Chrismettal/MiniMarquee/3D/PCB/v0.1/v0.1RenderBack.png

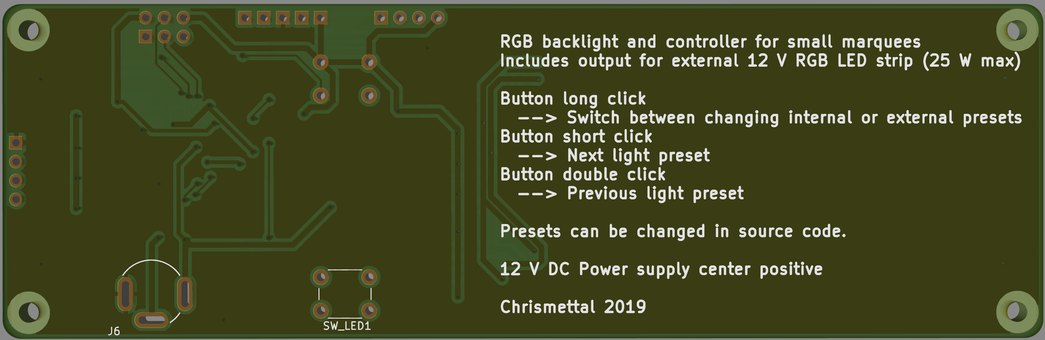
3D/PCB/v0.1/v0.1RenderBack.png
