Chrismettal/MiniMarquee/images/DC_Jack.jpg

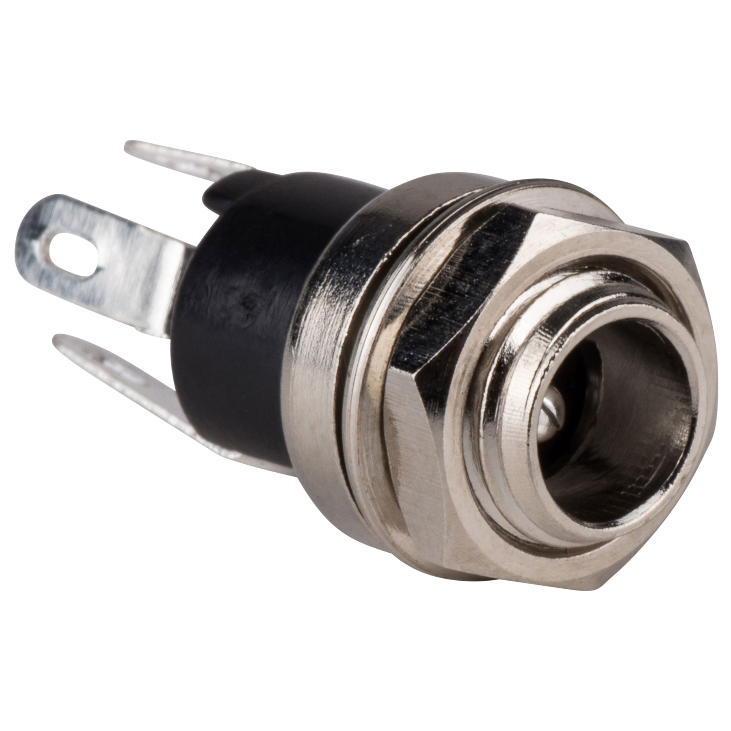
images/DC_Jack.jpg
