Chrismettal/MiniMarquee/images/PCB_placemap.png

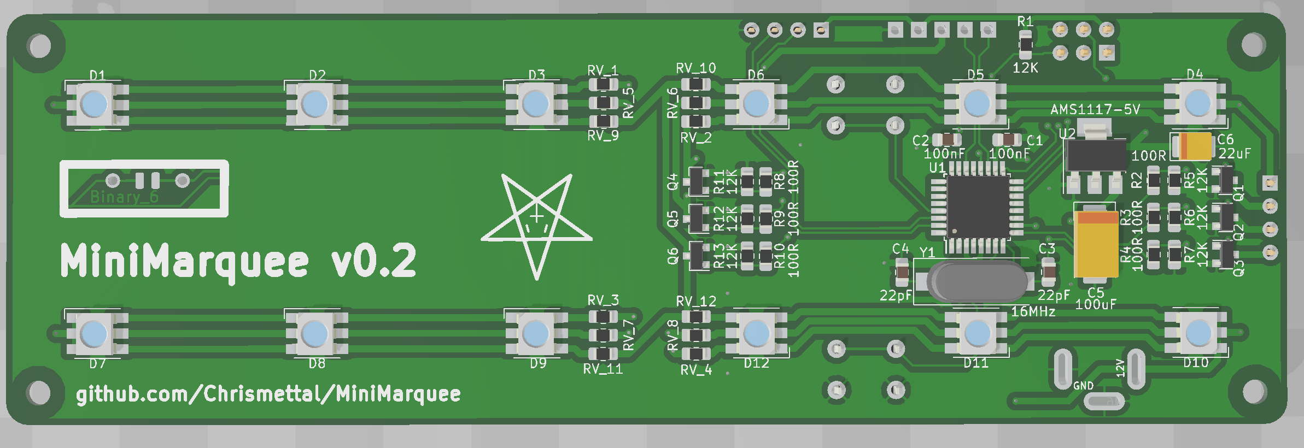
images/PCB_placemap.png
