Chrismettal/MiniMarquee/images/PCB_render1.png

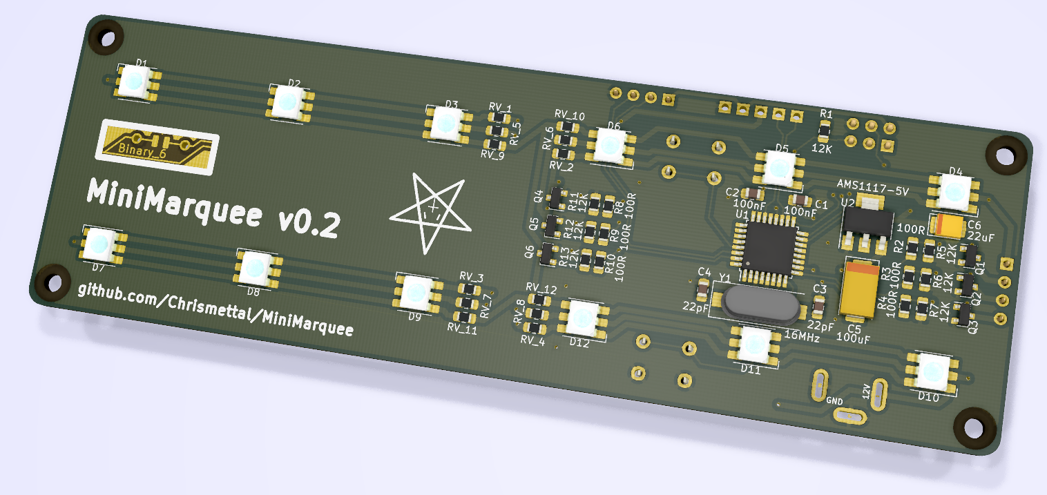
images/PCB_render1.png
