Chrismettal/MiniMarquee/images/PCB_render2.png

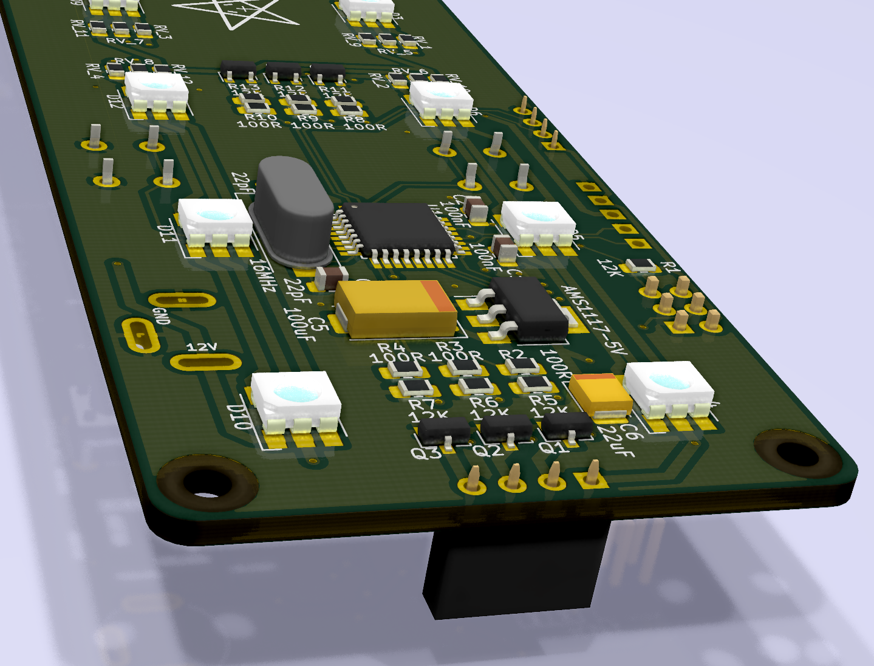
images/PCB_render2.png
