Chrismettal/MiniMarquee/3D/Printable_v0.2/Sony/PS2/PS2_clr.stl

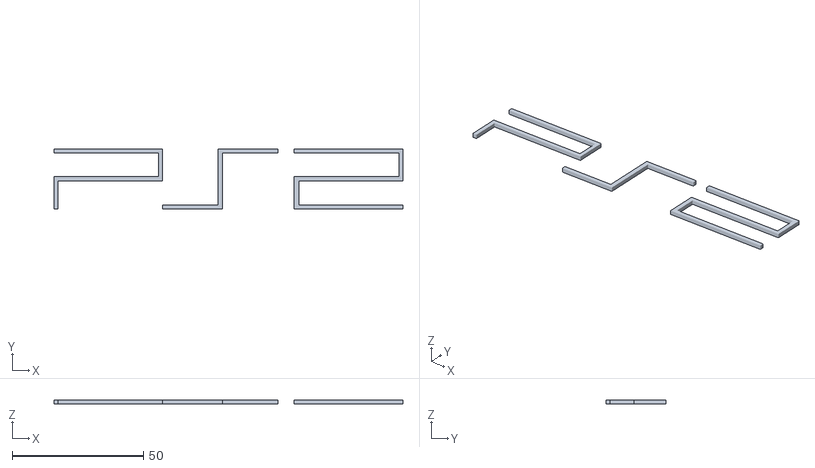
[picture p48: CAD file, 2019-06-09]
3D/Printable_v0.2/Sony/PS2/PS2_clr.stl
133.1 x 23.0 x 1.60
