Chrismettal/MiniMarquee/3D/Printable_v0.2/Sony/PS4/PS4_blu.stl

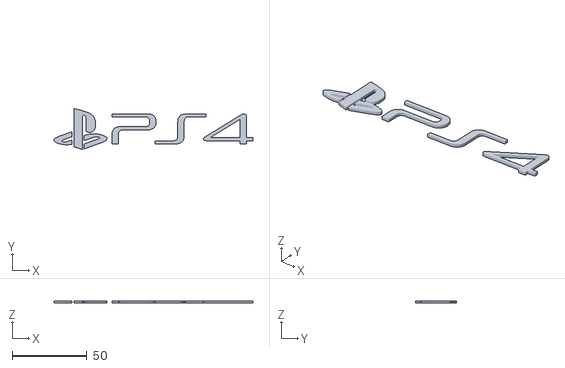
[picture p50: CAD file, 2019-06-01]
3D/Printable_v0.2/Sony/PS4/PS4_blu.stl
133.6 x 27.5 x 1.60
