Chrismettal/MiniMarquee/3D/Printable_v0.2/Atari/2600/2600_clr.stl

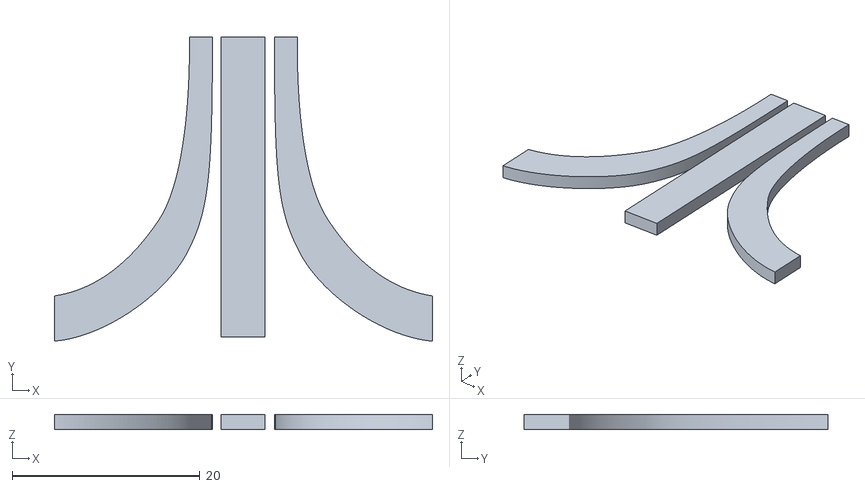
[picture p51: CAD file, 2019-06-20]
3D/Printable_v0.2/Atari/2600/2600_clr.stl
40.3 x 32.4 x 1.60
