Chrismettal/MiniMarquee/3D/Printable_v0.2/Diffusor_wh.stl

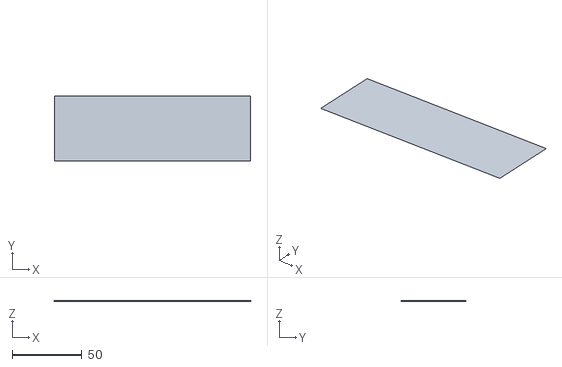
[picture p52: CAD file, 2019-06-21]
3D/Printable_v0.2/Diffusor_wh.stl
140.4 x 46.4 x 0.2
