Chrismettal/MiniMarquee/3D/Printable_v0.2/Microsoft/Xbox/Xbox_grn.stl

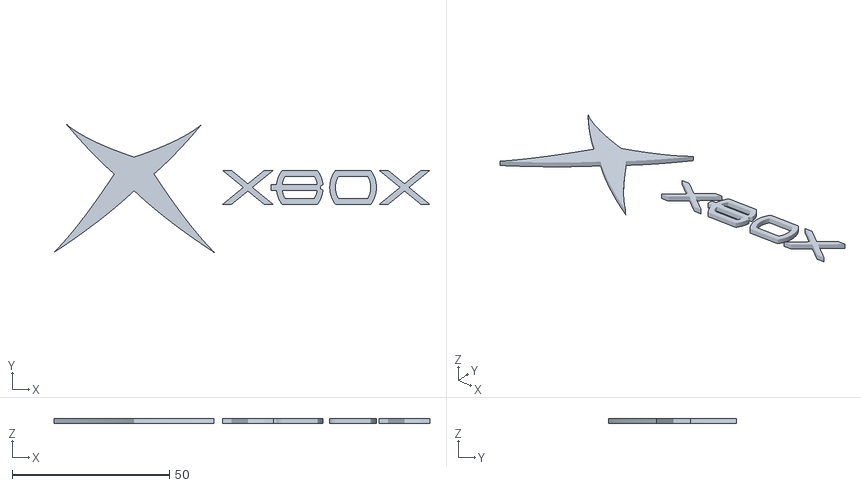
[picture p53: CAD file, 2019-06-10]
3D/Printable_v0.2/Microsoft/Xbox/Xbox_grn.stl
119.7 x 40.6 x 1.60
