Chrismettal/MiniMarquee/3D/Printable_v0.2/Microsoft/Xbox360/Xbox360_grn.stl

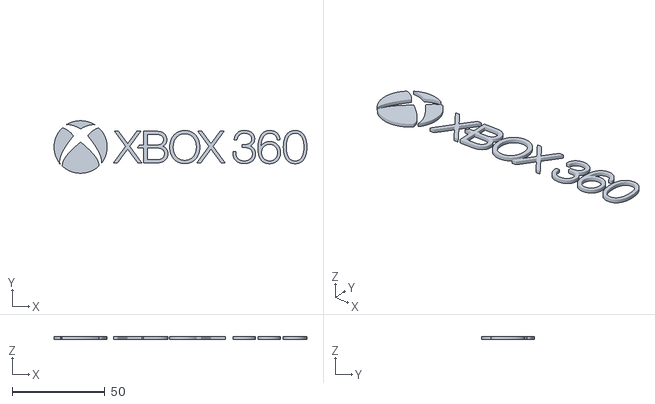
[picture p54: CAD file, 2019-06-10]
3D/Printable_v0.2/Microsoft/Xbox360/Xbox360_grn.stl
136.6 x 28.4 x 1.60
