Chrismettal/MiniMarquee/3D/Printable_v0.2/Nintendo/N64/N64_grn.stl

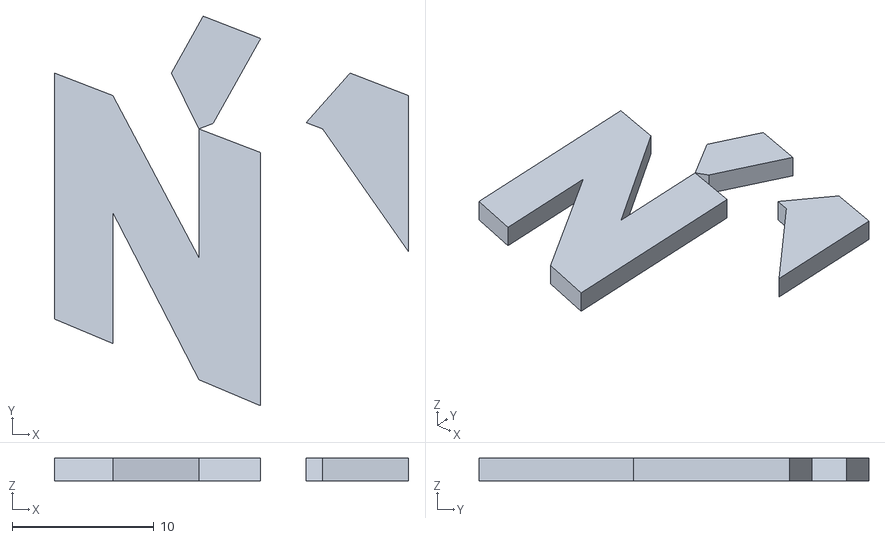
[picture p55: CAD file, 2019-06-09]
3D/Printable_v0.2/Nintendo/N64/N64_grn.stl
24.9 x 27.5 x 1.60
