Chrismettal/MiniMarquee/3D/Printable_v0.2/Nintendo/NES/NES_red.stl

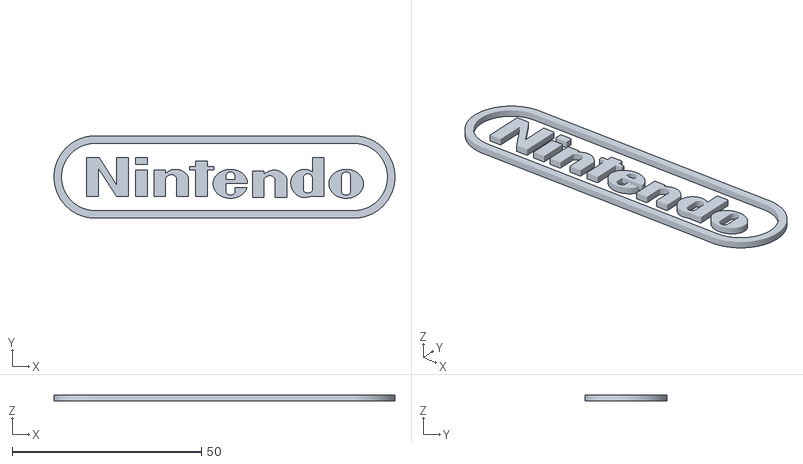
[picture p56: CAD file, 2019-06-09]
3D/Printable_v0.2/Nintendo/NES/NES_red.stl
90.0 x 21.7 x 1.60
