Chrismettal/MiniMarquee/3D/Printable_v0.2/Nintendo/SNES/SNES_wh.stl

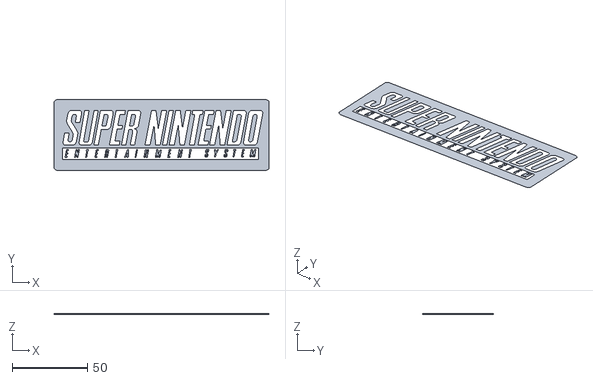
[picture p57: CAD file, 2019-06-09]
3D/Printable_v0.2/Nintendo/SNES/SNES_wh.stl
143.0 x 47.2 x 0.2
