Chrismettal/MiniMarquee/3D/Printable_v0.2/Nintendo/Wii/Wii_blk.stl

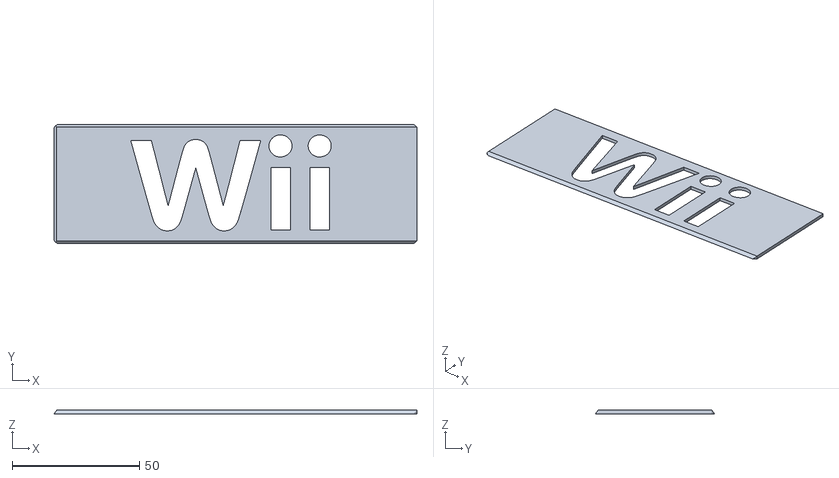
[picture p58: CAD file, 2019-06-09]
3D/Printable_v0.2/Nintendo/Wii/Wii_blk.stl
142.9 x 46.9 x 1.40
