Chrismettal/MiniMarquee/3D/Printable_v0.2/Nintendo/WiiU/WiiU_clr.stl

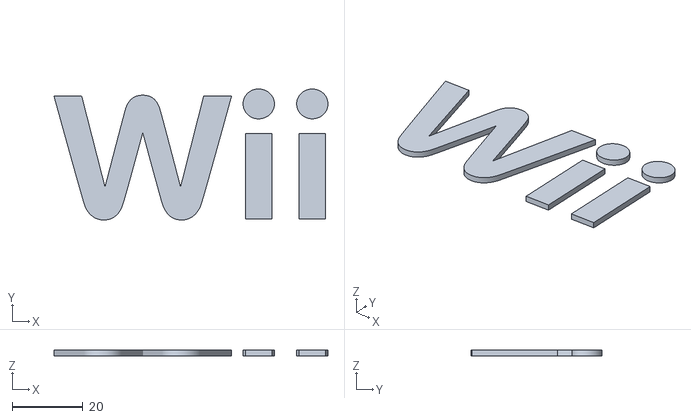
[picture p59: CAD file, 2019-06-09]
3D/Printable_v0.2/Nintendo/WiiU/WiiU_clr.stl
77.6 x 37.1 x 1.60
