Chrismettal/MiniMarquee/3D/Printable_v0.2/Sega/MasterSystem/Sega_MS_red.stl

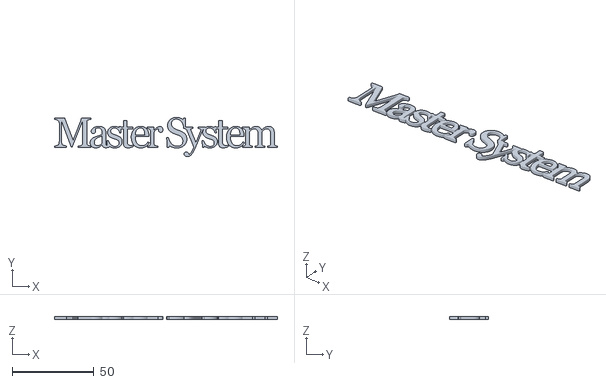
[picture p60: CAD file, 2019-06-20]
3D/Printable_v0.2/Sega/MasterSystem/Sega_MS_red.stl
136.0 x 24.0 x 1.60
