Chrismettal/MiniMarquee/3D/Printable_v0.2/Sony/PS2/PS2_wh.stl

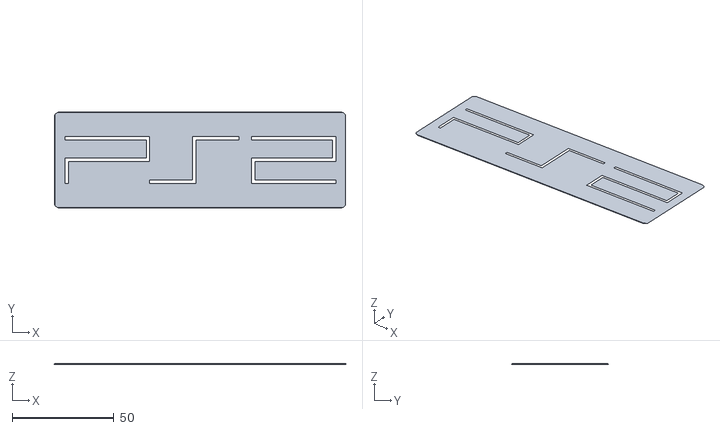
[picture p61: CAD file, 2019-06-09]
3D/Printable_v0.2/Sony/PS2/PS2_wh.stl
143.0 x 47.2 x 0.2
