Chrismettal/MiniMarquee/3D/Printable_v0.2/Microsoft/XboxOne/XboxOne_grn.stl

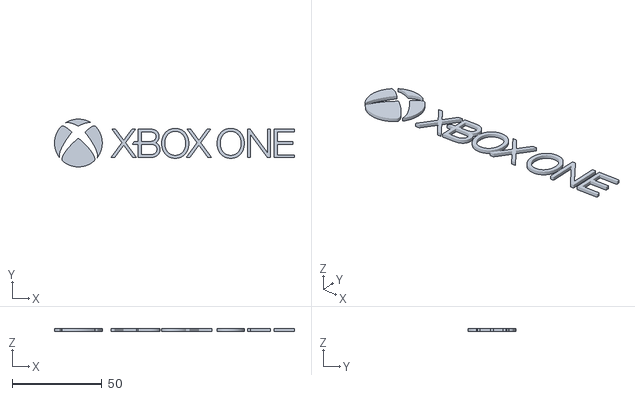
[picture p62: CAD file, 2019-06-10]
3D/Printable_v0.2/Microsoft/XboxOne/XboxOne_grn.stl
133.5 x 26.6 x 1.60
