Chrismettal/MiniMarquee/3D/Printable_v0.2/NeoGeo/NeoGeo_red.stl

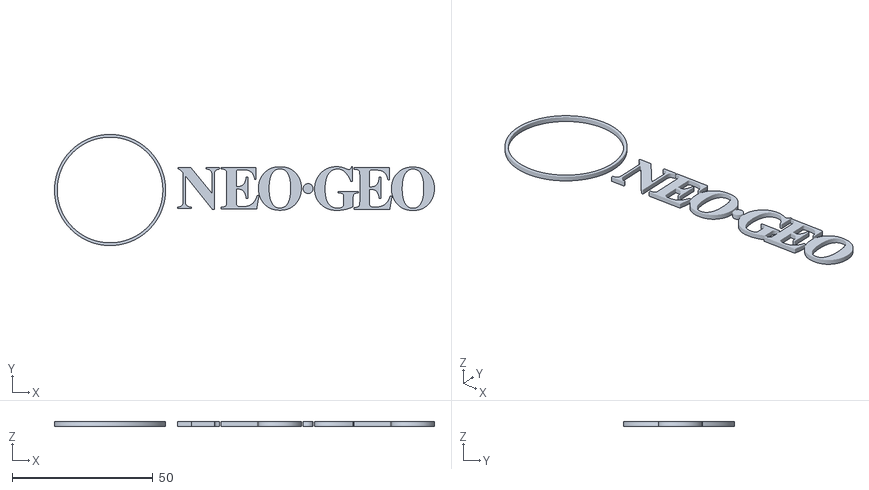
[picture p63: CAD file, 2019-06-20]
3D/Printable_v0.2/NeoGeo/NeoGeo_red.stl
134.9 x 39.4 x 1.60
