Chrismettal/MiniMarquee/3D/Printable_v0.2/Nintendo/GC/GC_blu.stl

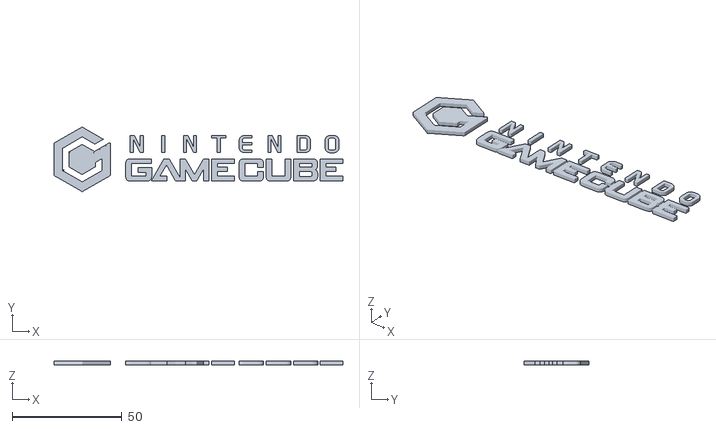
[picture p64: CAD file, 2019-06-09]
3D/Printable_v0.2/Nintendo/GC/GC_blu.stl
131.4 x 29.5 x 1.60
