Chrismettal/MiniMarquee/3D/Printable_v0.2/Nintendo/N64/N64_blk.stl

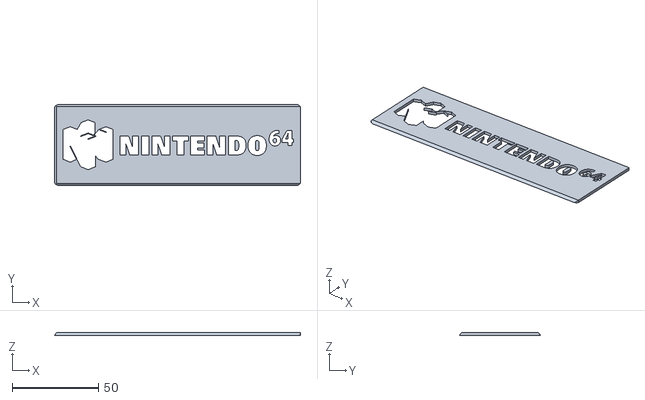
[picture p65: CAD file, 2019-06-09]
3D/Printable_v0.2/Nintendo/N64/N64_blk.stl
143.0 x 47.2 x 1.60
