Chrismettal/MiniMarquee/3D/Printable_v0.2/Nintendo/WiiU/WiiU_blk.stl

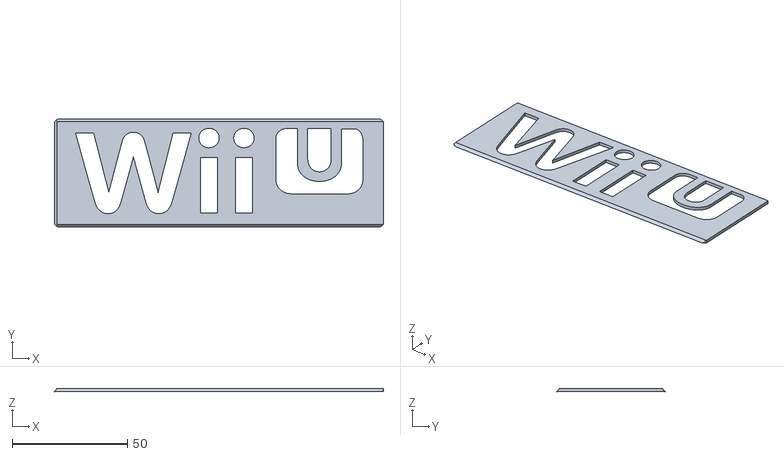
[picture p66: CAD file, 2019-06-09]
3D/Printable_v0.2/Nintendo/WiiU/WiiU_blk.stl
142.9 x 46.9 x 1.40
