Chrismettal/MiniMarquee/3D/Printable_v0.2/RawSign_blk.stl

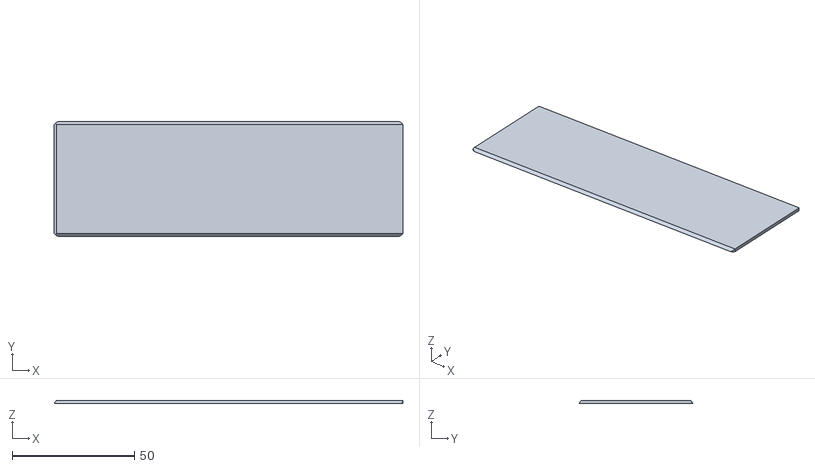
[picture p67: CAD file, 2019-06-10]
3D/Printable_v0.2/RawSign_blk.stl
142.9 x 46.9 x 1.40
