Chrismettal/MiniMarquee/3D/Printable_v0.2/Sony/PS1/PS1_blu.stl

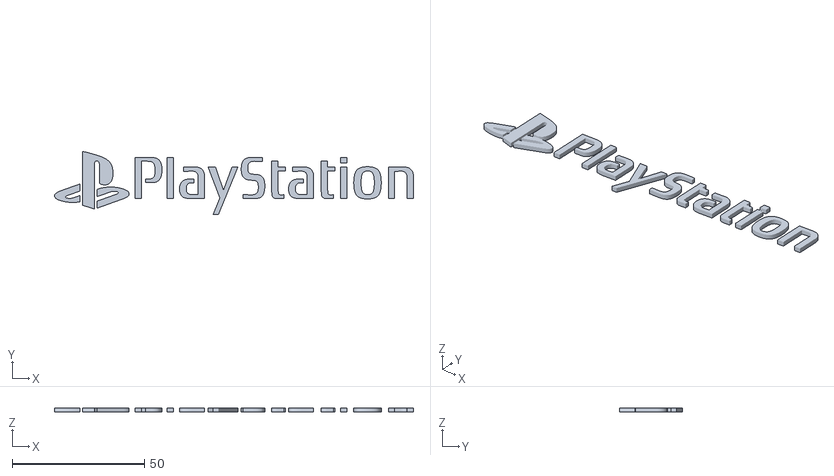
[picture p68: CAD file, 2019-06-09]
3D/Printable_v0.2/Sony/PS1/PS1_blu.stl
135.5 x 23.9 x 1.60
