Chrismettal/MiniMarquee/3D/Printable_v0.2/Sony/PS3/PS3_clr.stl

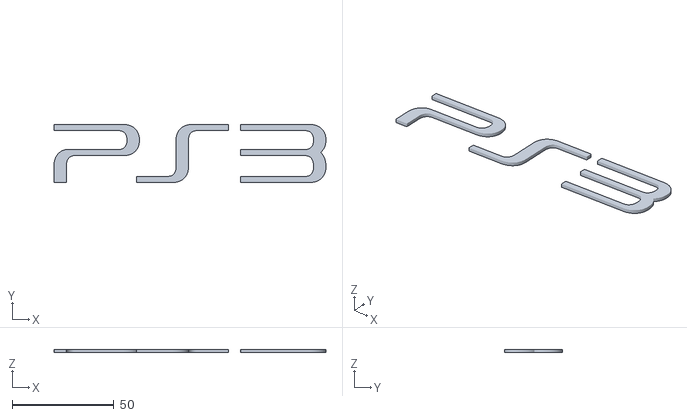
[picture p69: CAD file, 2019-06-09]
3D/Printable_v0.2/Sony/PS3/PS3_clr.stl
133.6 x 28.5 x 1.60
