Chrismettal/MiniMarquee/3D/Printable_v0.2/Commodore/Com_blu.stl

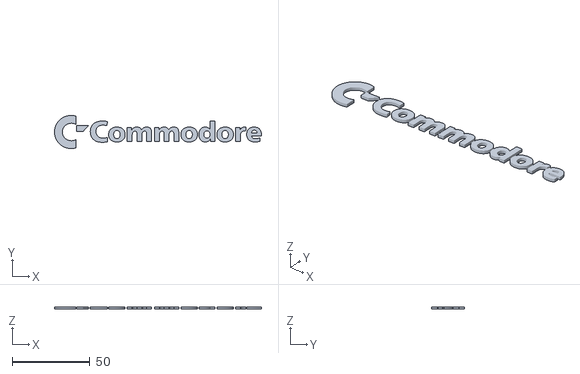
[picture p70: CAD file, 2019-06-20]
3D/Printable_v0.2/Commodore/Com_blu.stl
133.1 x 21.3 x 1.60
