Chrismettal/MiniMarquee/3D/Printable_v0.2/Nintendo/N64/N64_blu.stl

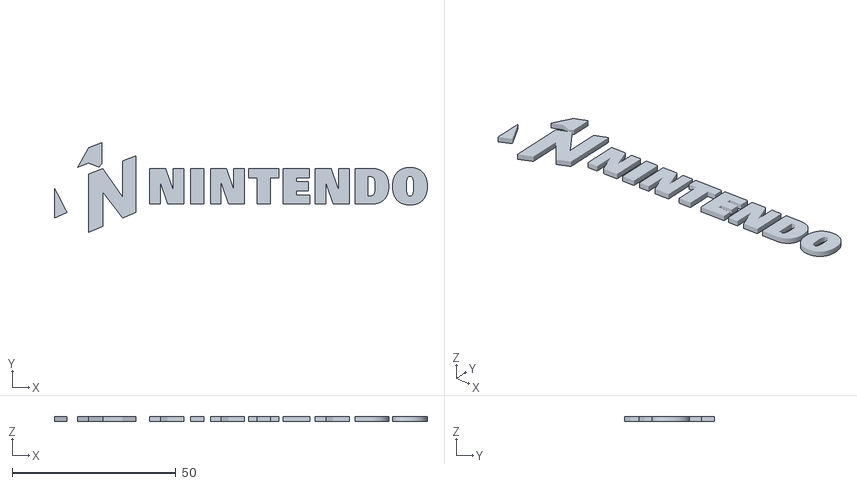
[picture p71: CAD file, 2019-06-09]
3D/Printable_v0.2/Nintendo/N64/N64_blu.stl
114.0 x 27.4 x 1.60
