Chrismettal/MiniMarquee/3D/Printable_v0.2/Nintendo/NES/NES_clr.stl

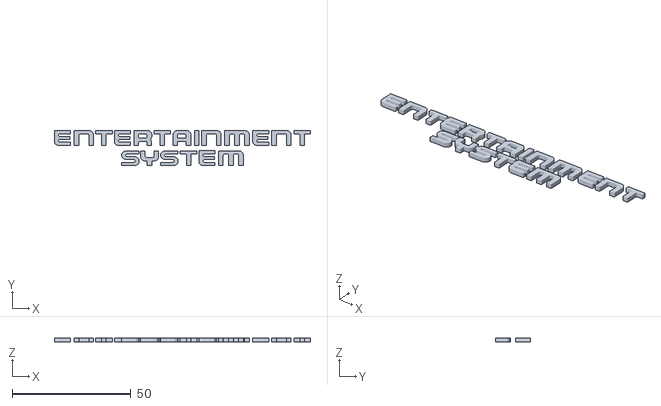
[picture p72: CAD file, 2019-06-09]
3D/Printable_v0.2/Nintendo/NES/NES_clr.stl
108.0 x 14.8 x 1.60
