Chrismettal/MiniMarquee/3D/Printable_v0.2/Nintendo/WiiU/WiiU_blu.stl

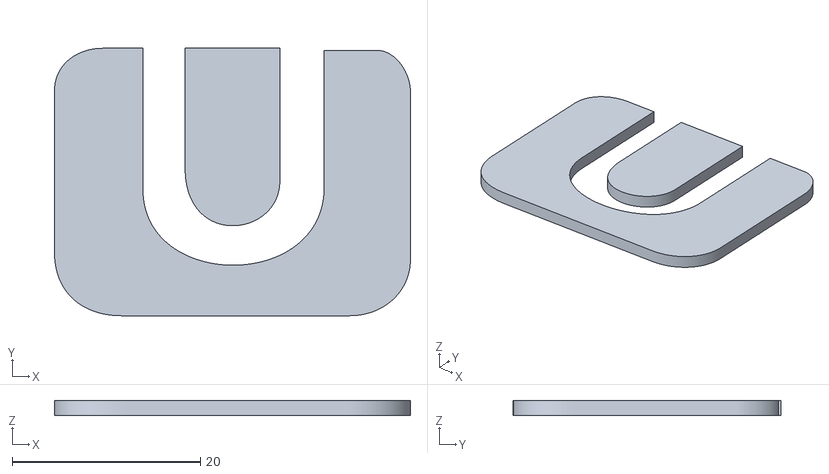
[picture p73: CAD file, 2019-06-09]
3D/Printable_v0.2/Nintendo/WiiU/WiiU_blu.stl
37.8 x 28.4 x 1.60
