Chrismettal/MiniMarquee/3D/Printable_v0.2/RawSign_wh.stl

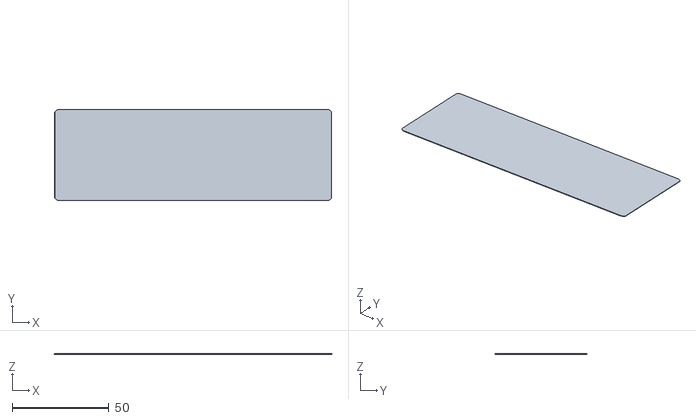
[picture p74: CAD file, 2019-06-10]
3D/Printable_v0.2/RawSign_wh.stl
143.0 x 47.2 x 0.2
