Chrismettal/MiniMarquee/3D/Printable_v0.2/Sega/MasterSystem/Sega_MS_blu.stl

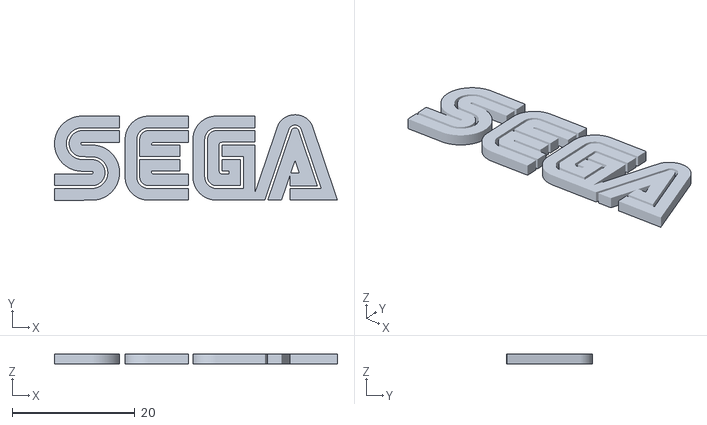
[picture p75: CAD file, 2019-06-20]
3D/Printable_v0.2/Sega/MasterSystem/Sega_MS_blu.stl
46.1 x 13.9 x 1.60
