Chrismettal/MiniMarquee/3D/Printable_v0.2/NeoGeo/NeoGeo_yel.stl

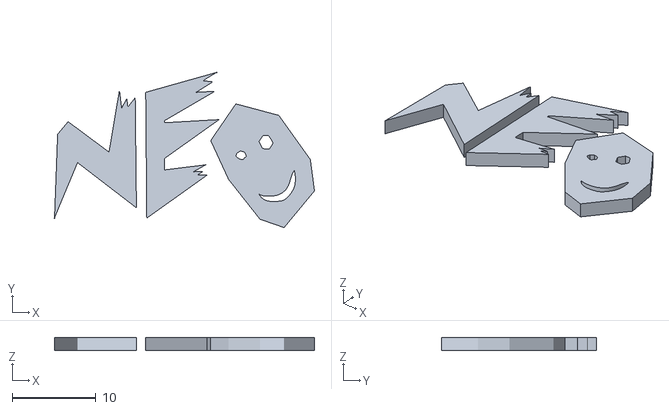
[picture p76: CAD file, 2019-06-20]
3D/Printable_v0.2/NeoGeo/NeoGeo_yel.stl
31.0 x 18.5 x 1.60
