Chrismettal/MiniMarquee/3D/Printable_v0.2/Nintendo/N64/N64_red.stl

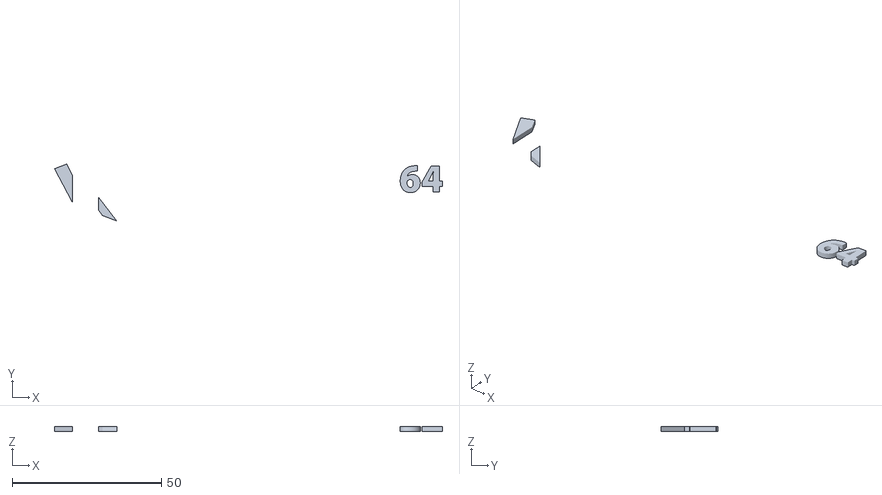
[picture p77: CAD file, 2019-06-09]
3D/Printable_v0.2/Nintendo/N64/N64_red.stl
129.8 x 19.1 x 1.60
