Chrismettal/MiniMarquee/images/Manual1.jpg

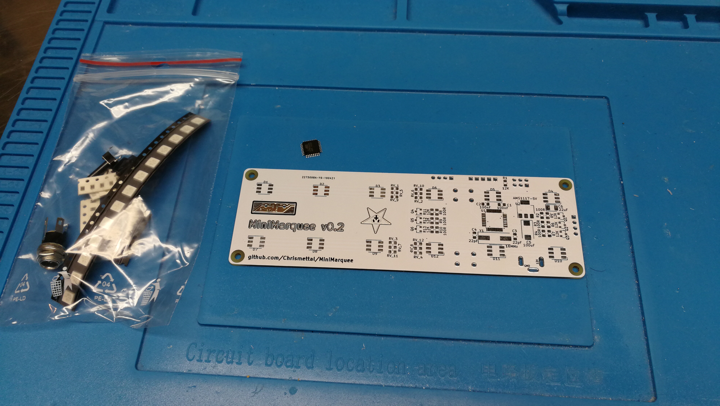
images/Manual1.jpg
