Chrismettal/MiniMarquee/images/Manual3.jpg

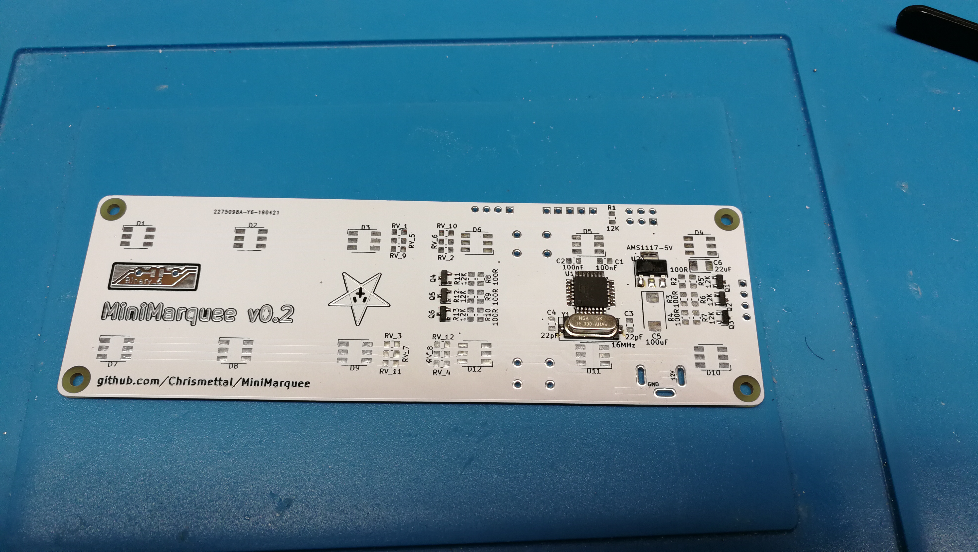
images/Manual3.jpg
