Chrismettal/MiniMarquee/images/Manual5.jpg

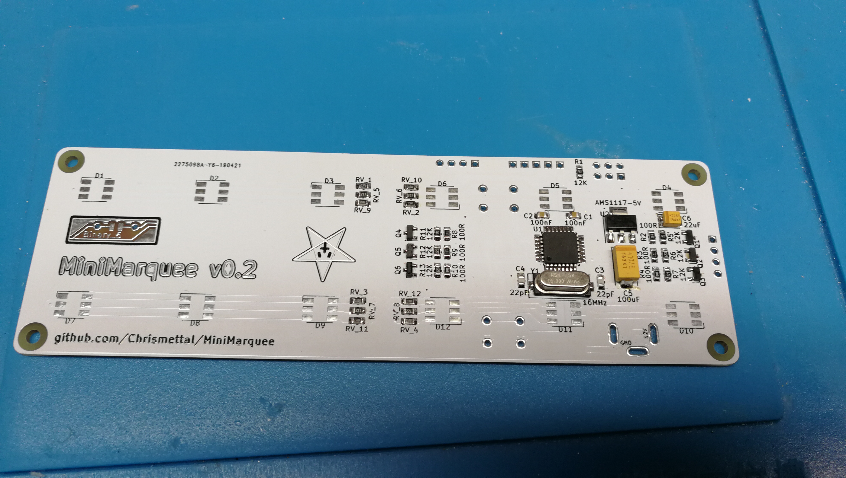
images/Manual5.jpg
