Chrismettal/MiniMarquee/images/Manual6.jpg

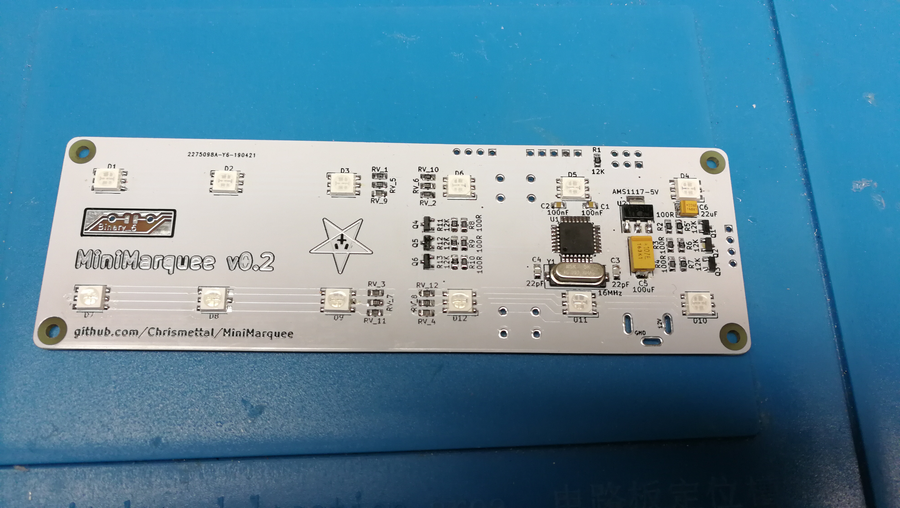
images/Manual6.jpg
