Chrismettal/MiniMarquee/images/Manual7.jpg

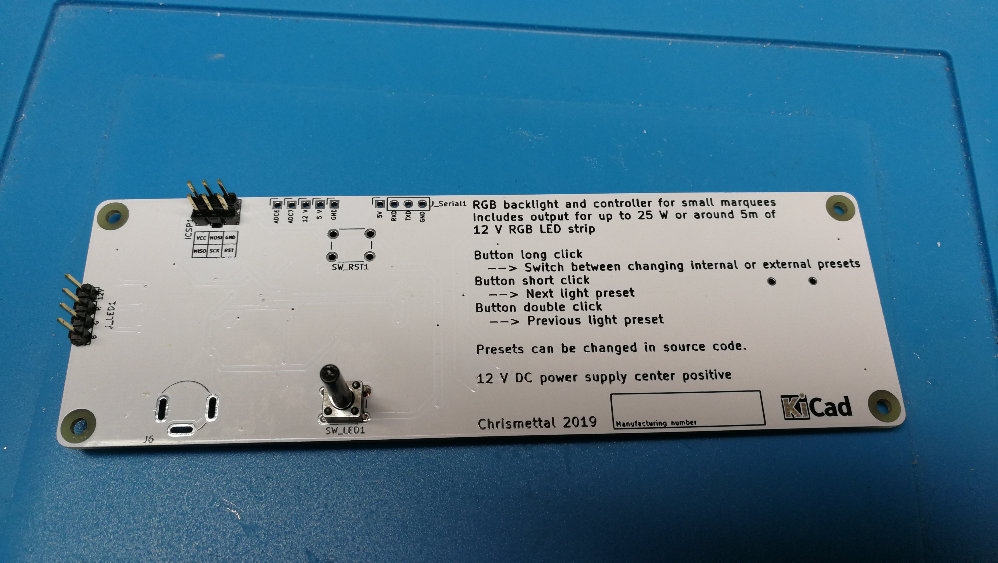
images/Manual7.jpg
