Chrismettal/MiniMarquee/images/Manual8.jpg

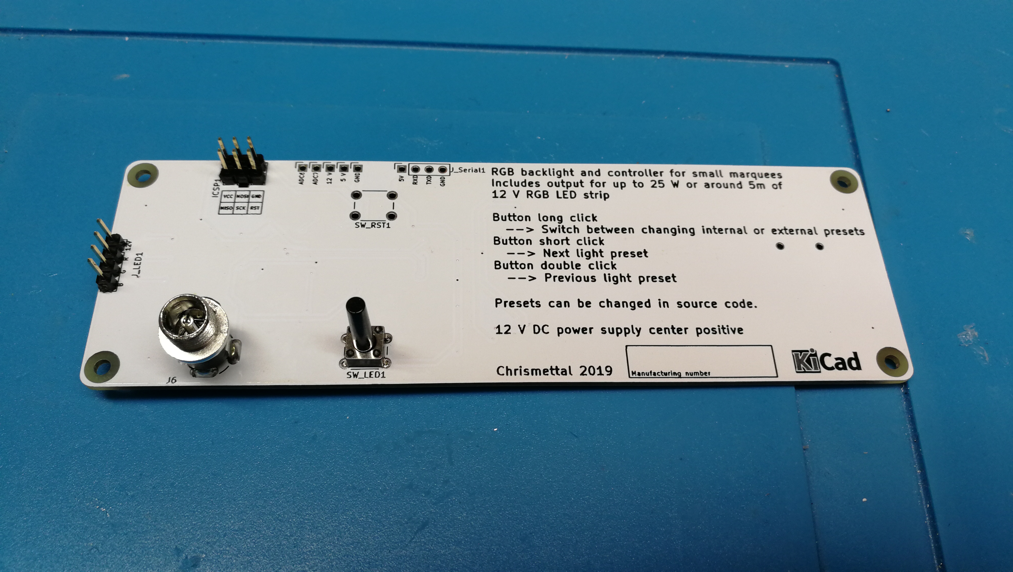
images/Manual8.jpg
